urielcontardi/DRSSTC/implementation/cleanup/bottom.png

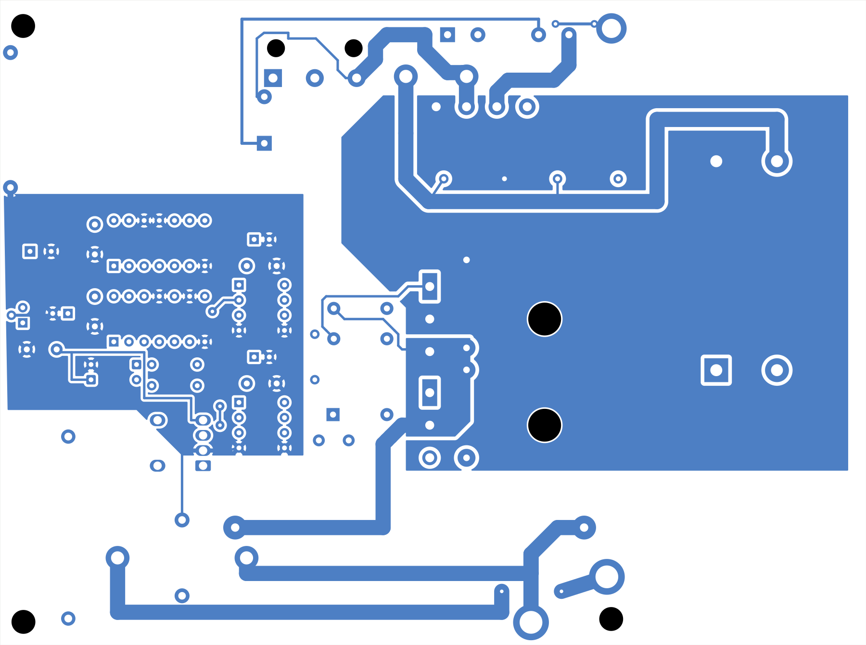
implementation/cleanup/bottom.png
