urielcontardi/DRSSTC/implementation/cleanup/top.png

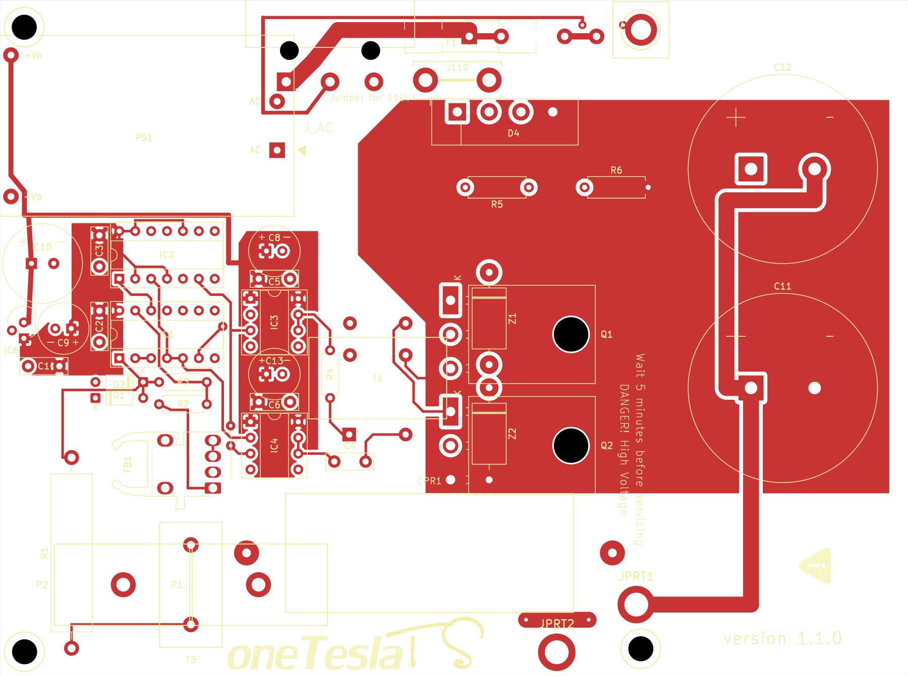
implementation/cleanup/top.png
