urielcontardi/DRSSTC/implementation/evidence/before-after.png

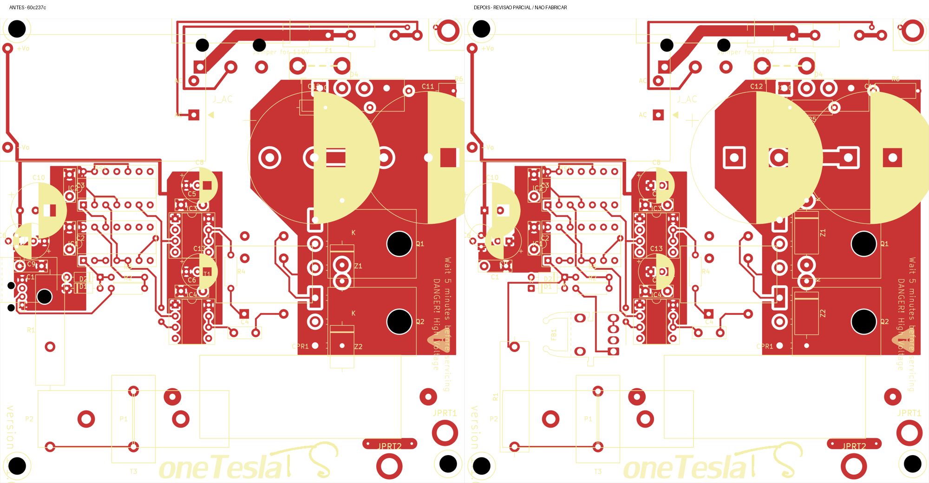
implementation/evidence/before-after.png
