urielcontardi/DRSSTC/implementation/evidence/bottom.png

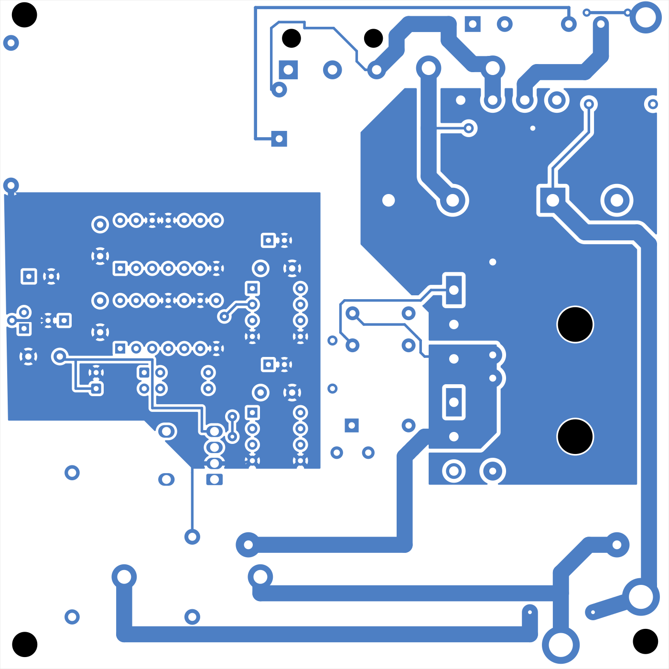
implementation/evidence/bottom.png
