urielcontardi/DRSSTC/implementation/evidence/top.png

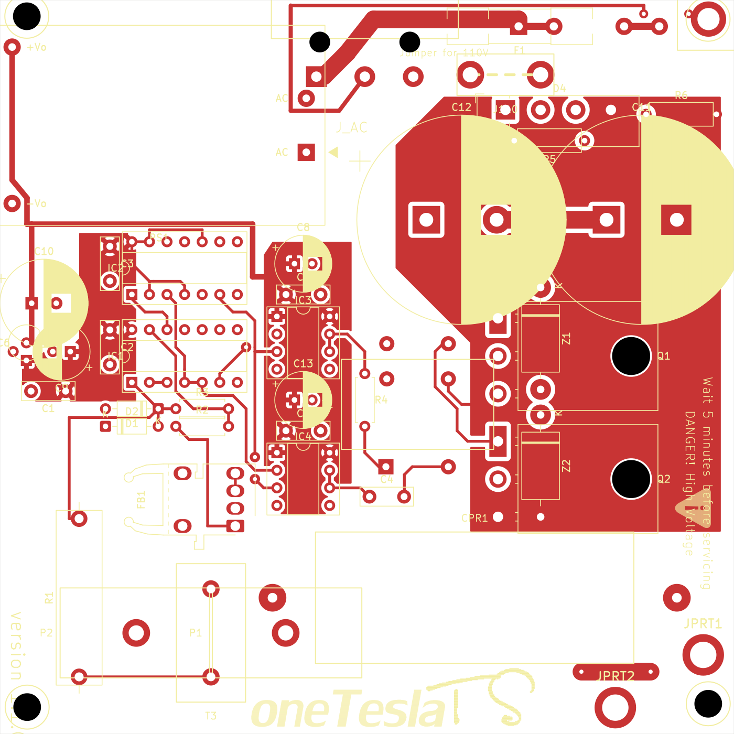
implementation/evidence/top.png
