urielcontardi/DRSSTC/implementation/expansion/before-after.png

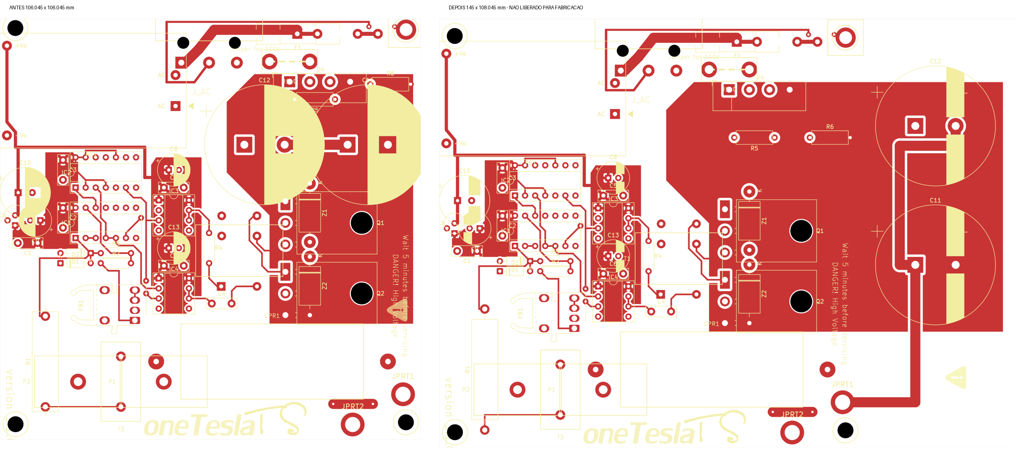
implementation/expansion/before-after.png
