urielcontardi/DRSSTC/misc/layout_ref.png

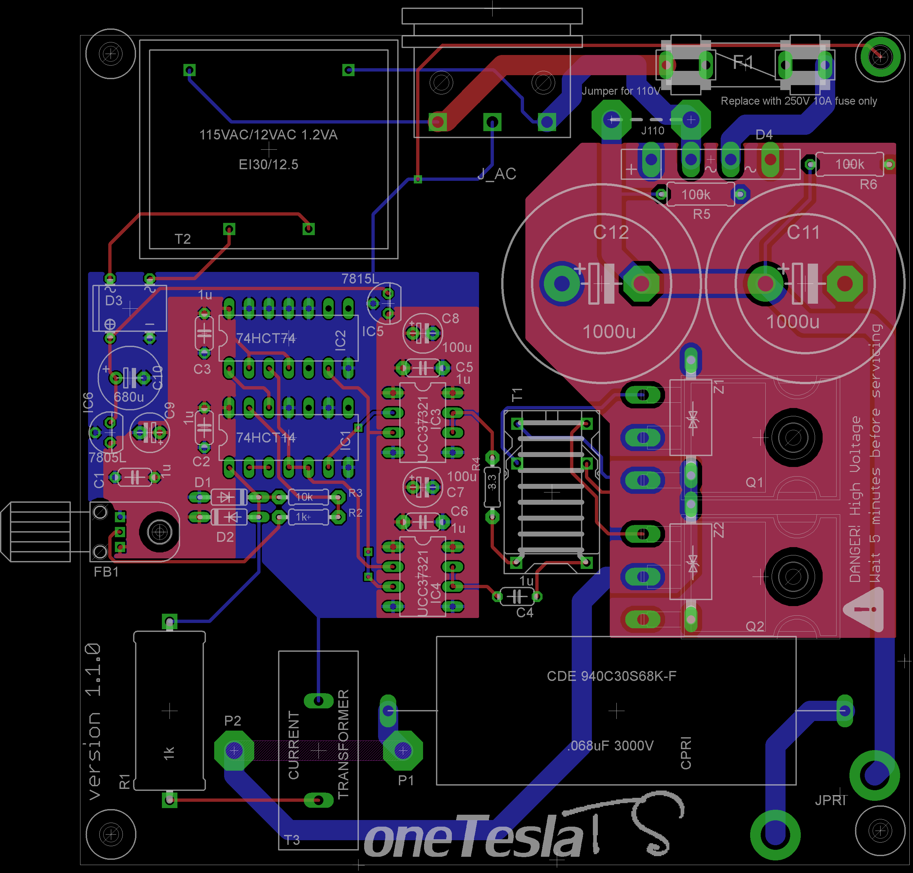
misc/layout_ref.png
