urielcontardi/DRSSTC/review/evidence/eagle-top.png

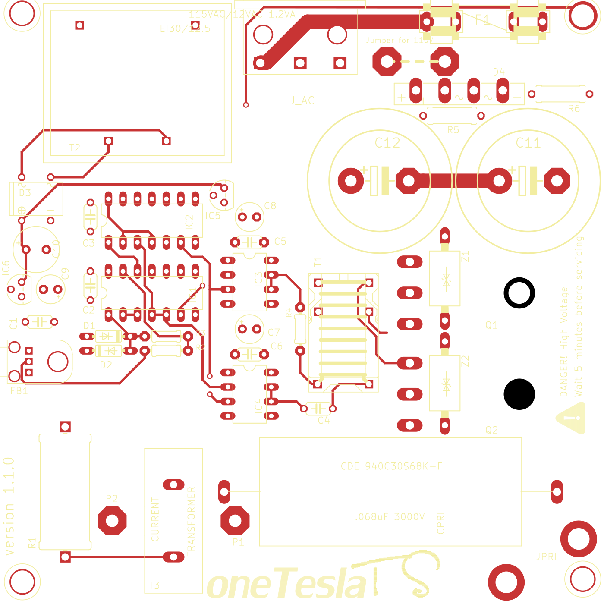
review/evidence/eagle-top.png
