urielcontardi/DRSSTC/review/evidence/top.png

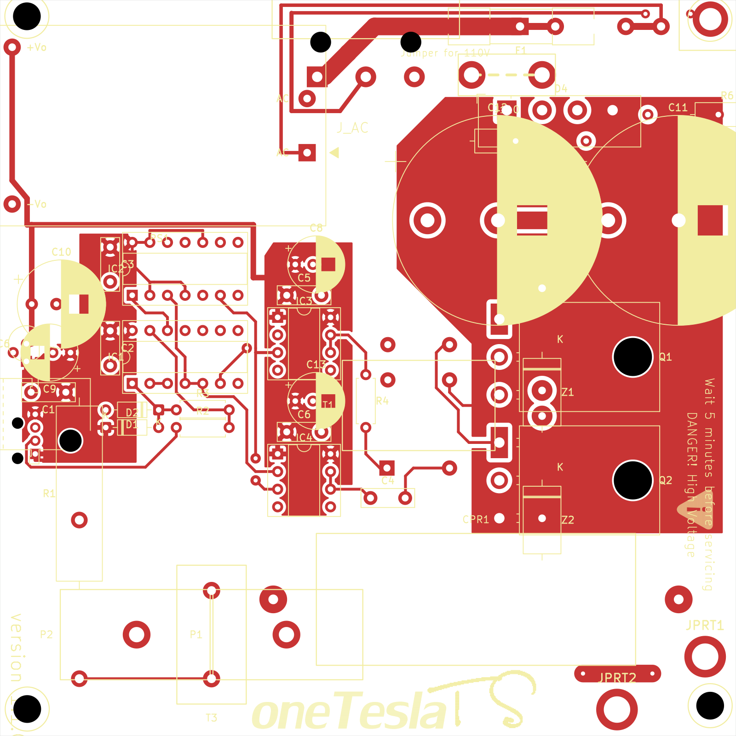
review/evidence/top.png
