urielcontardi/DRSSTC/implementation/cleanup/assembly.png

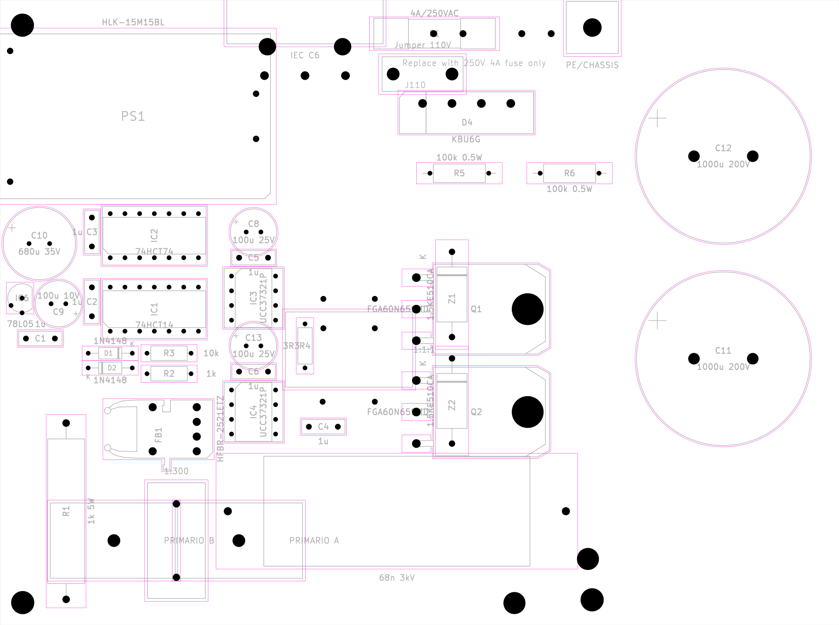
implementation/cleanup/assembly.png
