urielcontardi/DRSSTC/implementation/evidence/assembly.png

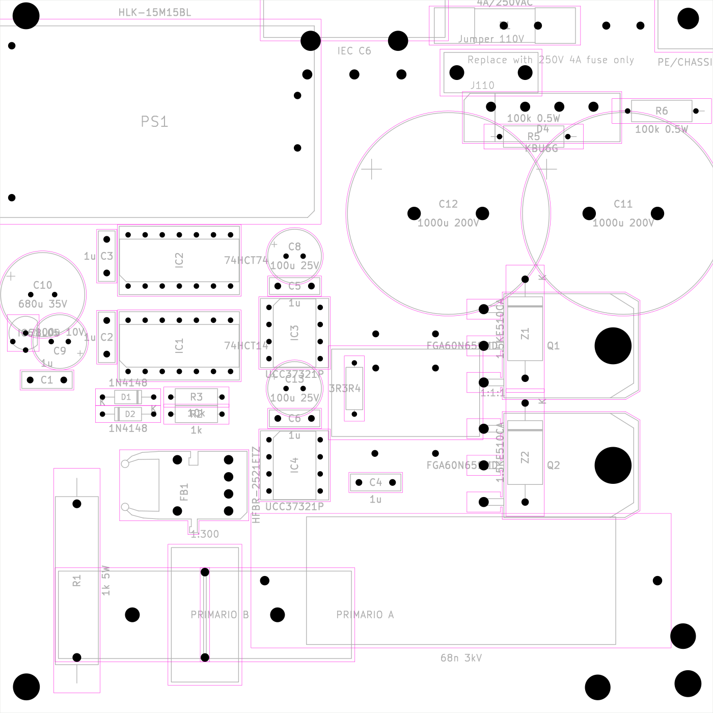
implementation/evidence/assembly.png
