urielcontardi/DRSSTC/implementation/layout_proposal/assembly.png

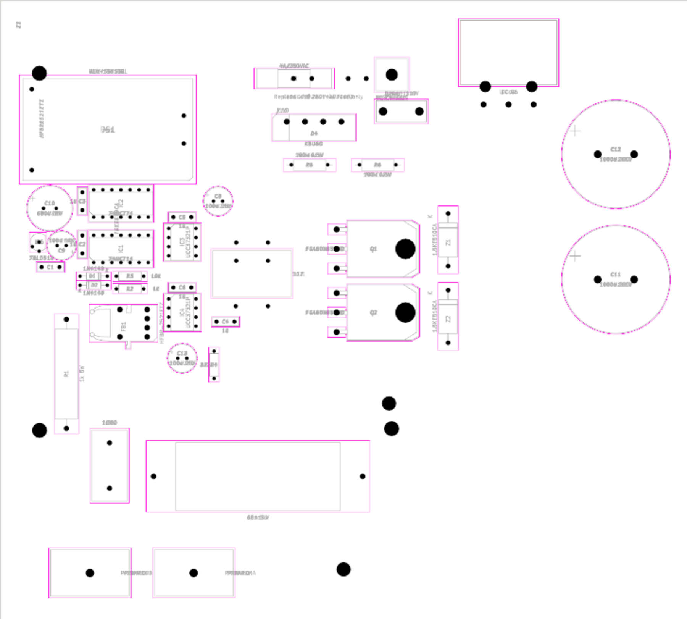
implementation/layout_proposal/assembly.png
