urielcontardi/DRSSTC/review/evidence/assembly.png

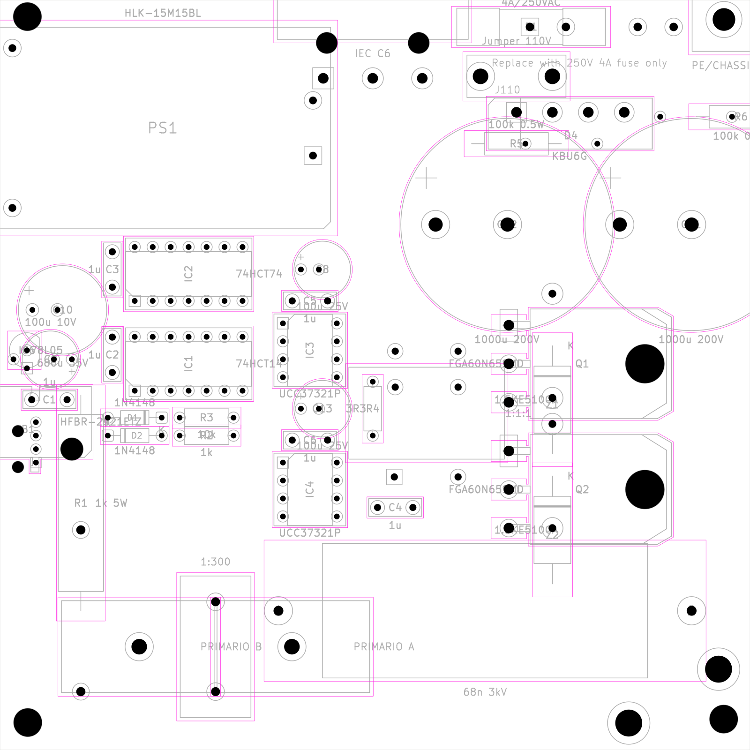
review/evidence/assembly.png
